Marsu31/HomeAutomation-RemoteControl/src/remote-control/main/include/sleep.h

/*
 * power_management.h
 *
 *  Created on: 11 nov. 2019
 *      Author: gabe
 */

#ifndef MAIN_INCLUDE_SLEEP_H_
#define MAIN_INCLUDE_SLEEP_H_

#include "buttons.h"

void init_hibernation();

#endif /* MAIN_INCLUDE_SLEEP_H_ */
